pangodream/Claudio/box/ClaudioBoxBase.jpg

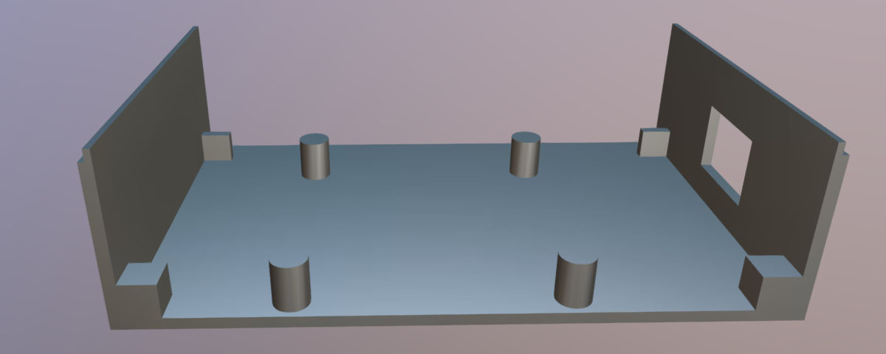
box/ClaudioBoxBase.jpg
