pangodream/Claudio/box/ClaudioBoxCover.jpg

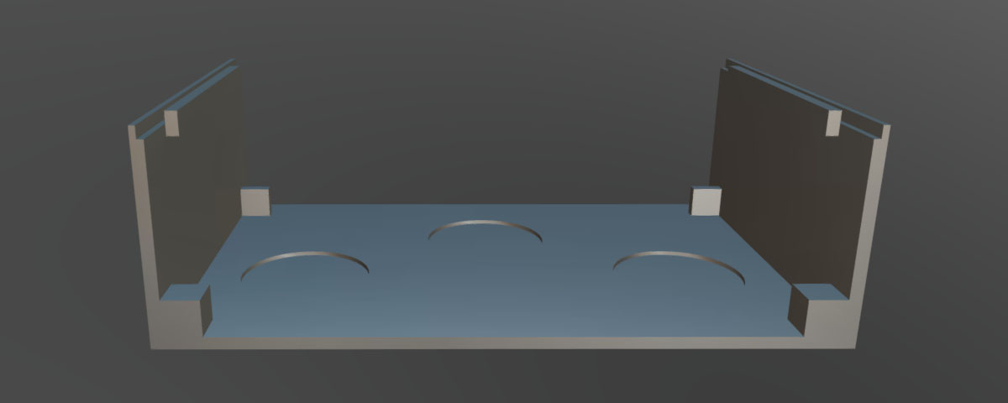
box/ClaudioBoxCover.jpg
