pangodream/Claudio/box/ClaudioBoxFront.jpg

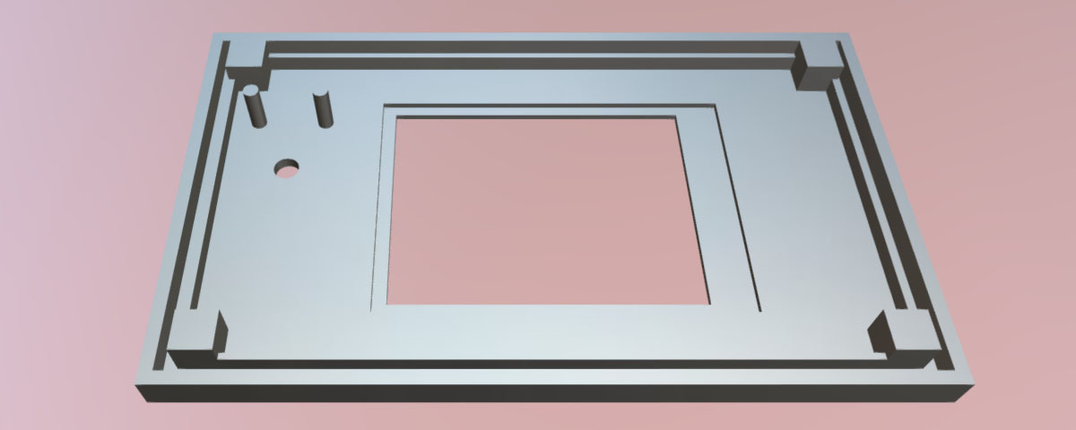
box/ClaudioBoxFront.jpg
